jmtritch/COSMOS22-Cluster13/1-boat/boat-team-images/boat-pulling-bouy.jpg

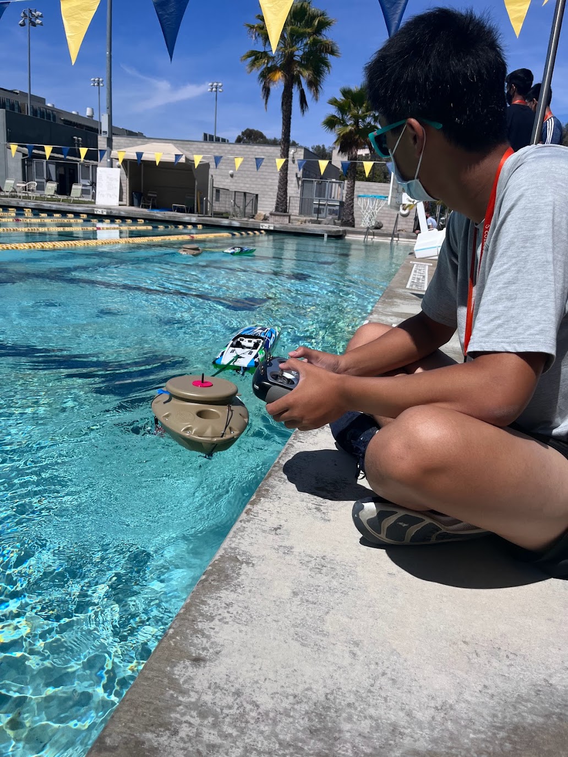
1-boat/boat-team-images/boat-pulling-bouy.jpg
