jmtritch/COSMOS22-Cluster13/1-boat/boat-team-images/broken-propellers.jpg

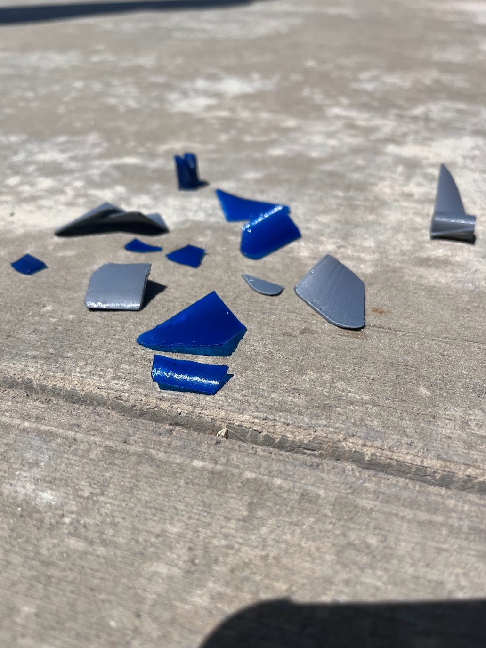
1-boat/boat-team-images/broken-propellers.jpg
