jmtritch/COSMOS22-Cluster13/1-boat/boat-team-images/fc-enclosure-fasteners.jpg

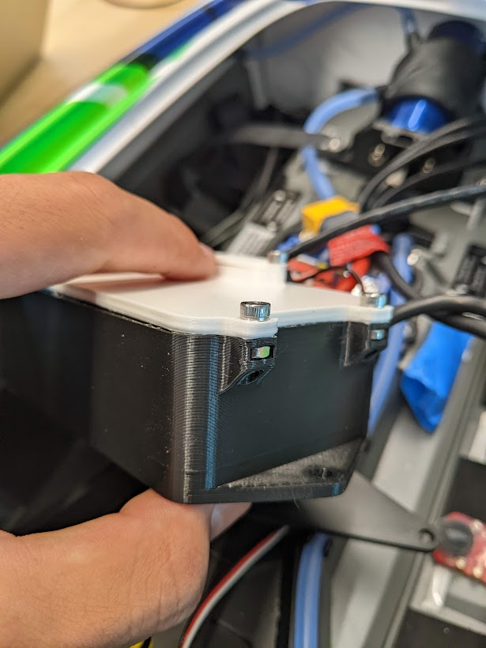
1-boat/boat-team-images/fc-enclosure-fasteners.jpg
