jmtritch/COSMOS22-Cluster13/1-boat/boat-team-images/fc-enclosure-mount-mounted.jpg

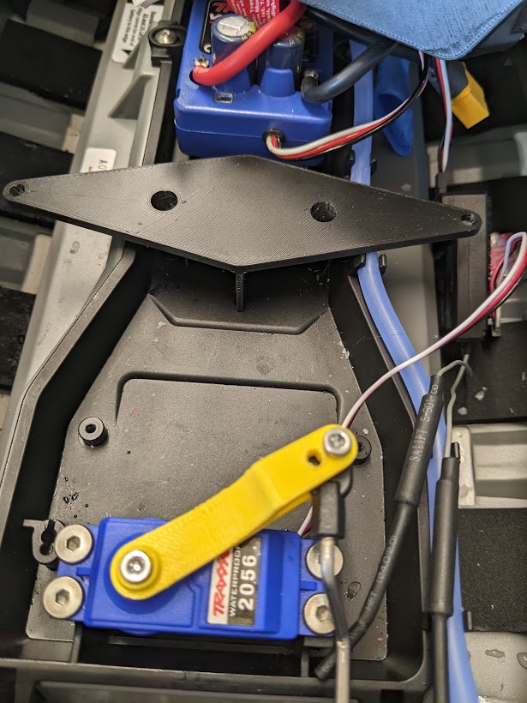
1-boat/boat-team-images/fc-enclosure-mount-mounted.jpg
