jmtritch/COSMOS22-Cluster13/1-boat/boat-team-images/fc-enclosure-wire-entry.jpg

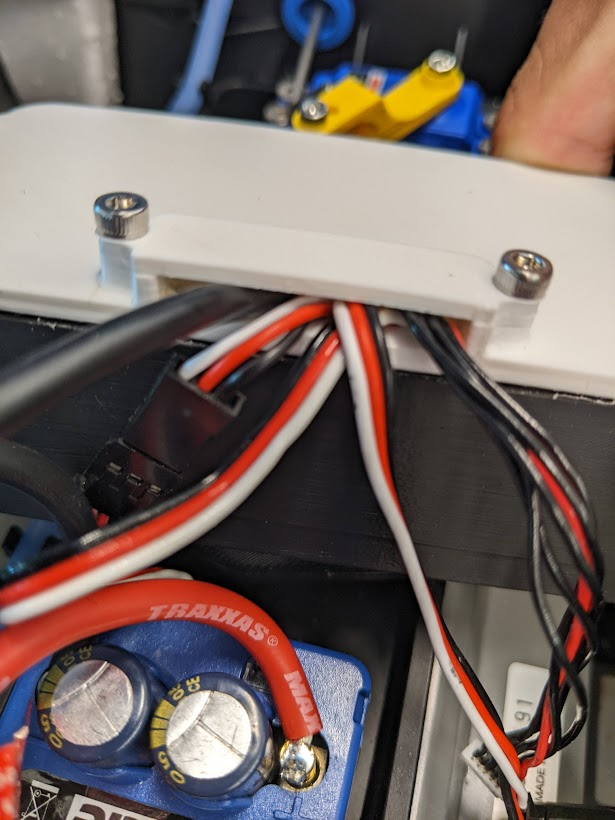
1-boat/boat-team-images/fc-enclosure-wire-entry.jpg
