jmtritch/COSMOS22-Cluster13/1-boat/boat-team-images/fc-sik-radio.jpg

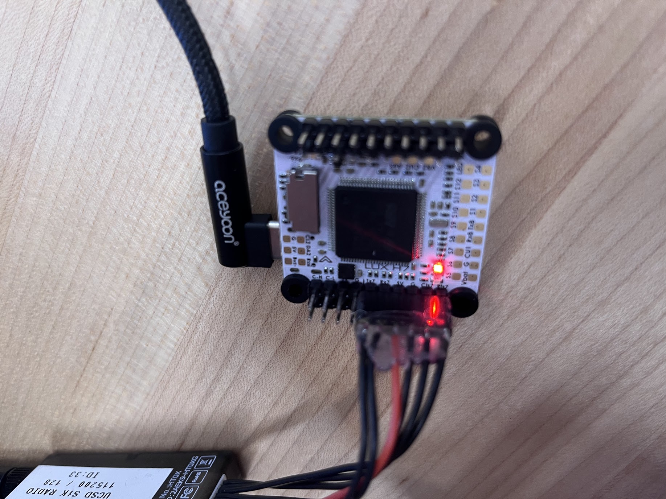
1-boat/boat-team-images/fc-sik-radio.jpg
