jmtritch/COSMOS22-Cluster13/1-boat/boat-team-images/gps-internals.jpg

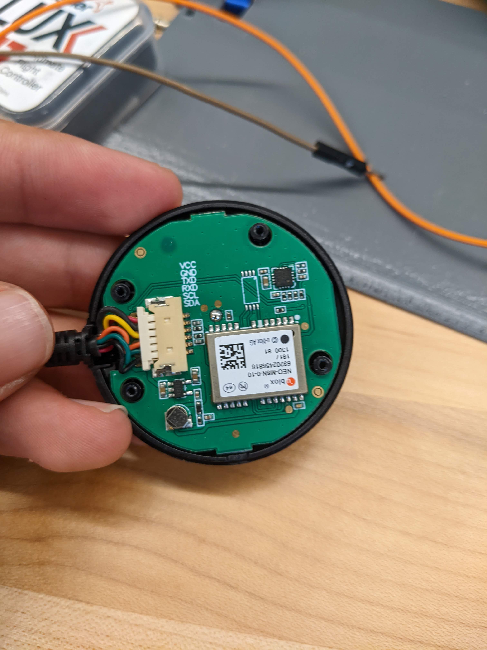
1-boat/boat-team-images/gps-internals.jpg
