jmtritch/COSMOS22-Cluster13/1-boat/boat-team-images/lake-day.jpg

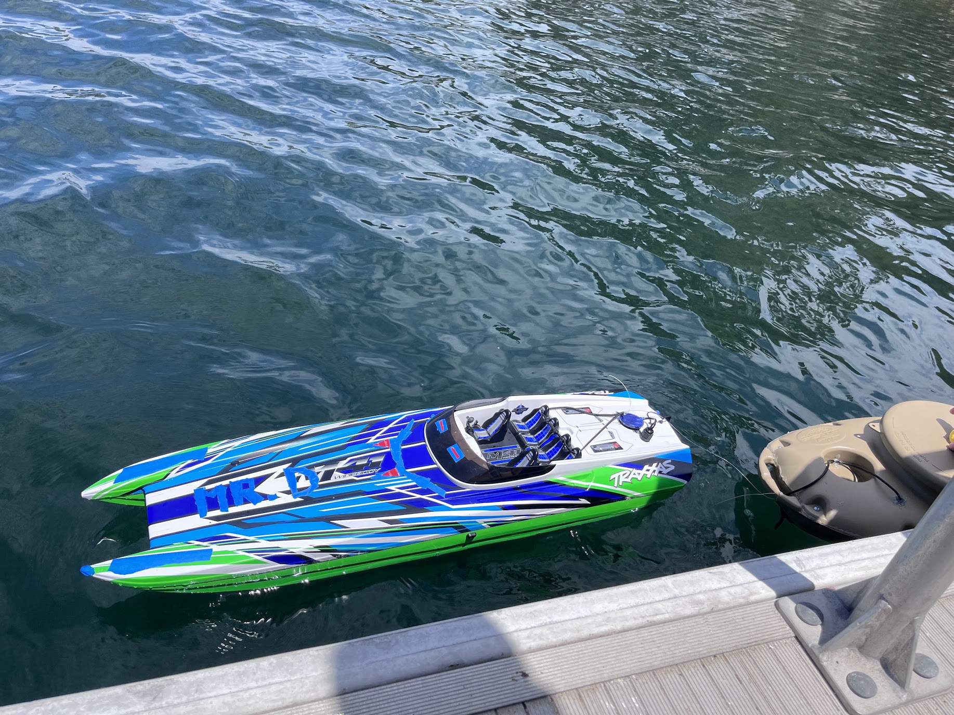
1-boat/boat-team-images/lake-day.jpg
