jmtritch/COSMOS22-Cluster13/1-boat/boat-team-images/pairing-radio.jpg

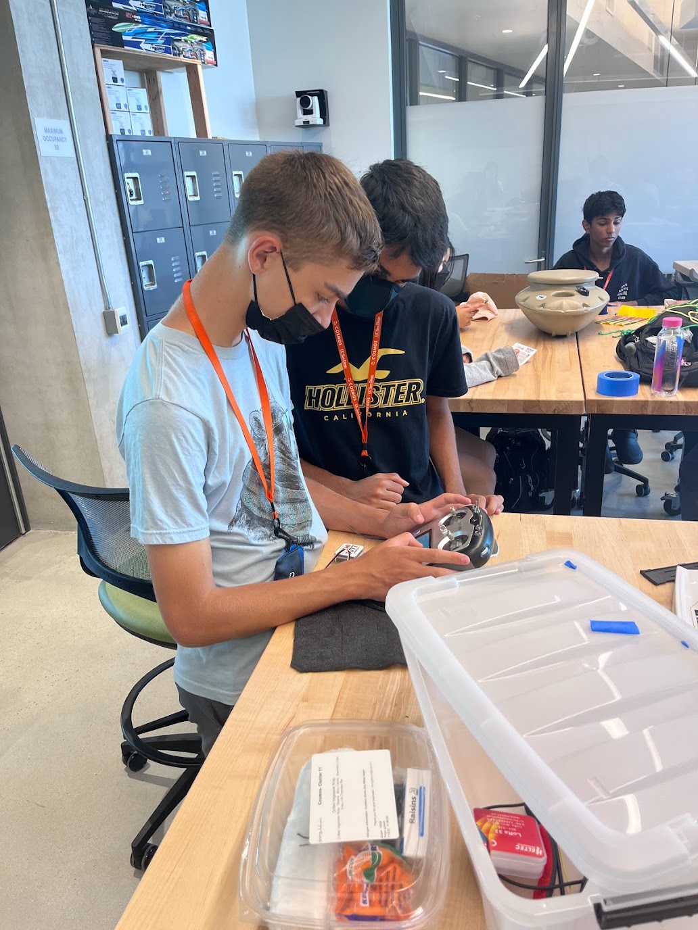
1-boat/boat-team-images/pairing-radio.jpg
