jmtritch/COSMOS22-Cluster13/1-boat/boat-team-images/rudder-iterations.jpg

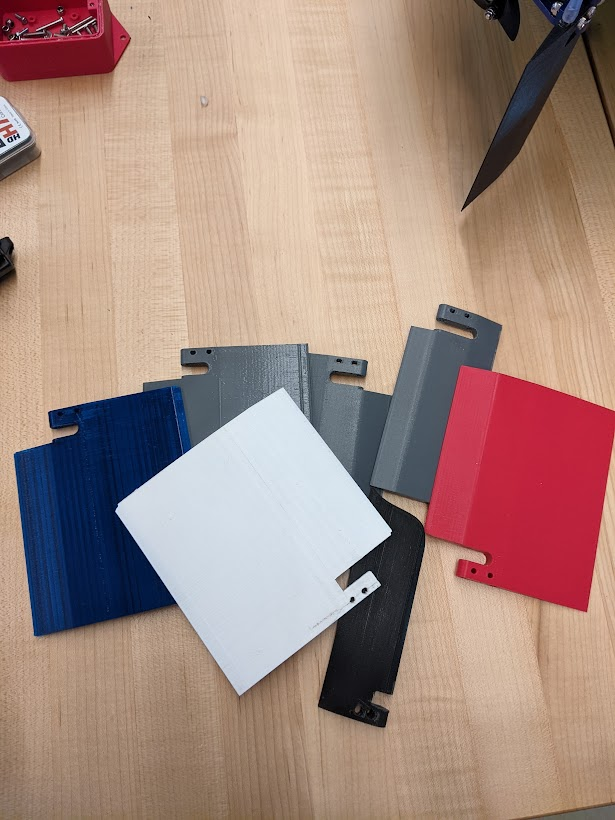
1-boat/boat-team-images/rudder-iterations.jpg
