jmtritch/COSMOS22-Cluster13/1-boat/boat-team-images/rudder-mod.jpg

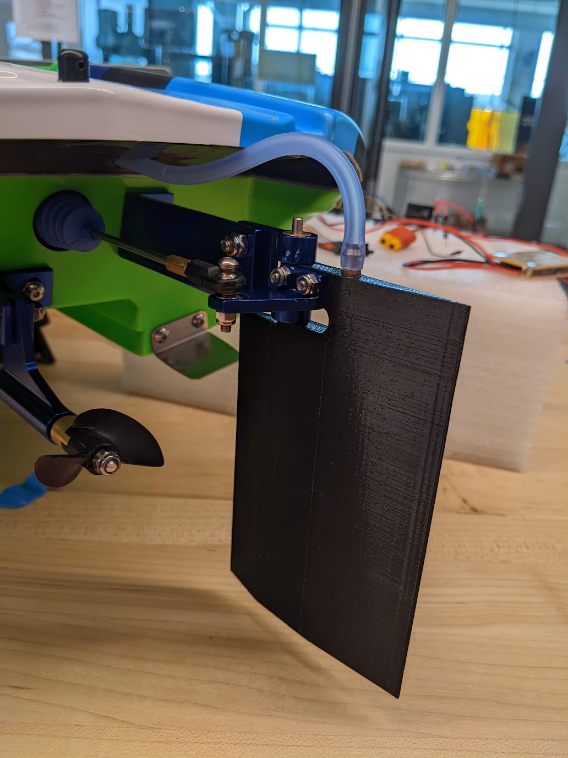
1-boat/boat-team-images/rudder-mod.jpg
