jmtritch/COSMOS22-Cluster13/2-buoy/Buoy1/Ph sensor.step

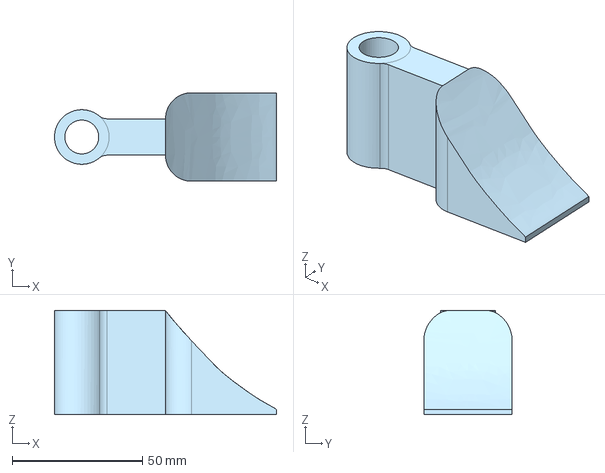
[picture p62: CAD file, 2022-08-02]
2-buoy/Buoy1/Ph sensor.step
85.3 x 34.0 x 40.0 mm
