jmtritch/COSMOS22-Cluster13/2-buoy/Buoy1/TDS Sensor base.step

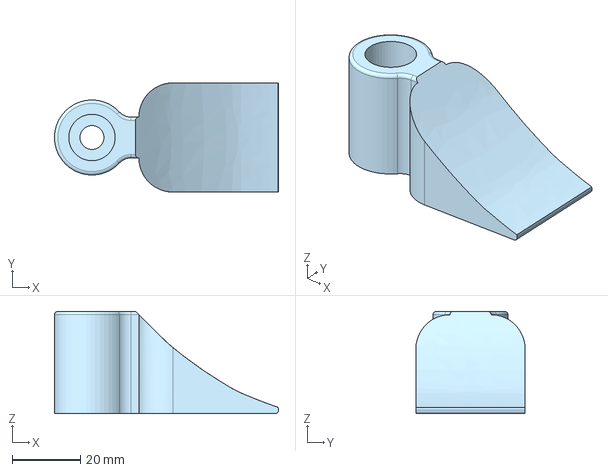
[picture p63: CAD file, 2022-08-02]
2-buoy/Buoy1/TDS Sensor base.step
65.7 x 32.0 x 30.0 mm
