jmtritch/COSMOS22-Cluster13/2-buoy/Buoy1/Temperature holder.step

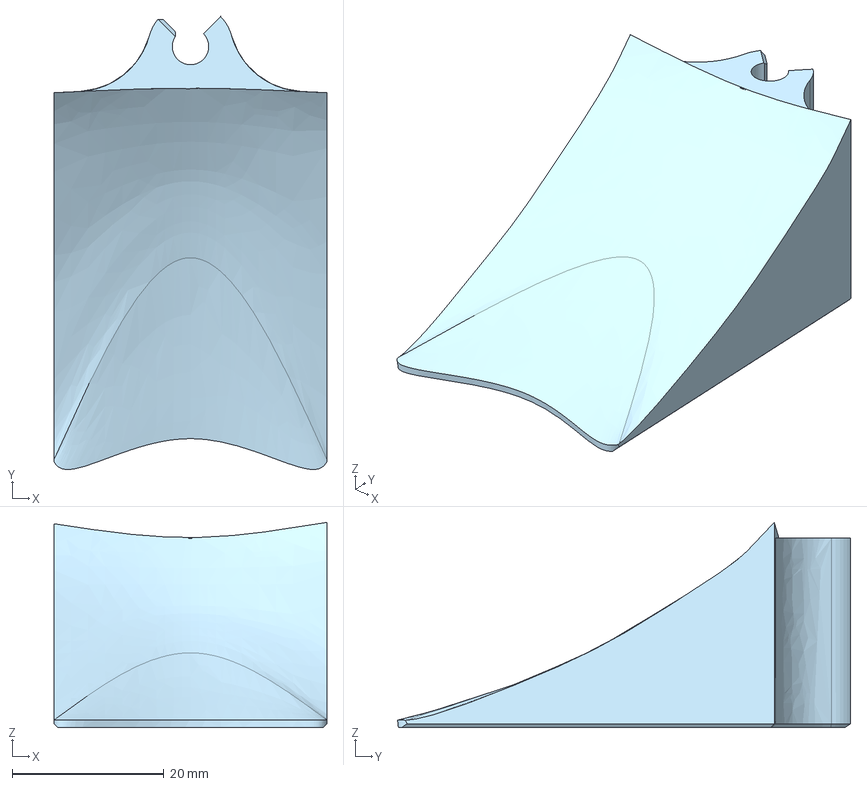
[picture p64: CAD file, 2022-08-02]
2-buoy/Buoy1/Temperature holder.step
36.0 x 59.7 x 27.1 mm
