jmtritch/COSMOS22-Cluster13/2-buoy/Buoy1/TDS sensor enclosure.step

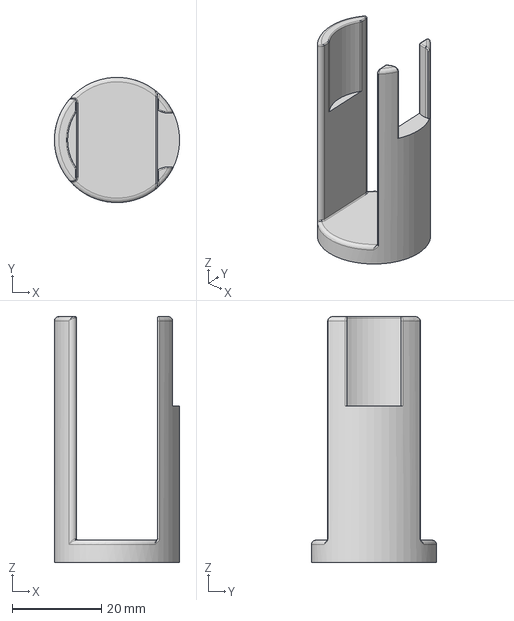
[picture p65: CAD file, 2022-08-02]
2-buoy/Buoy1/TDS sensor enclosure.step
28.0 x 28.0 x 55.0 mm
